ioprojecton/800W-load_bank/images/ac-dc.jpeg

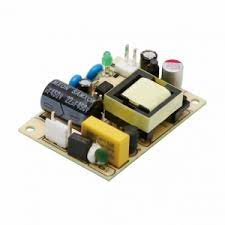
images/ac-dc.jpeg
