ioprojecton/800W-load_bank/images/fuse.jpeg

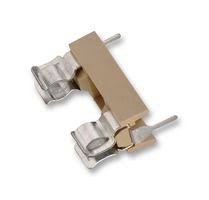
images/fuse.jpeg
