ioprojecton/800W-load_bank/images/LHD-03-TS.jpg

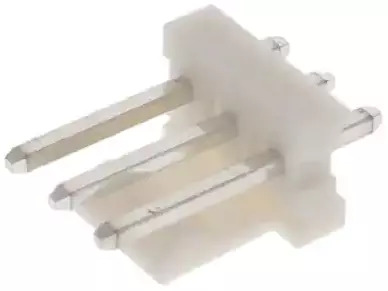
images/LHD-03-TS.jpg
