ioprojecton/800W-load_bank/images/npn.jpg

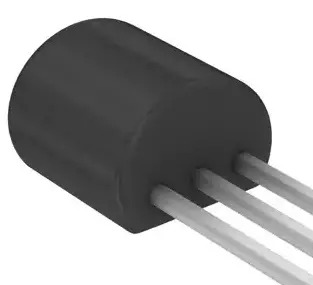
images/npn.jpg
