ioprojecton/800W-load_bank/images/resistor.jpg

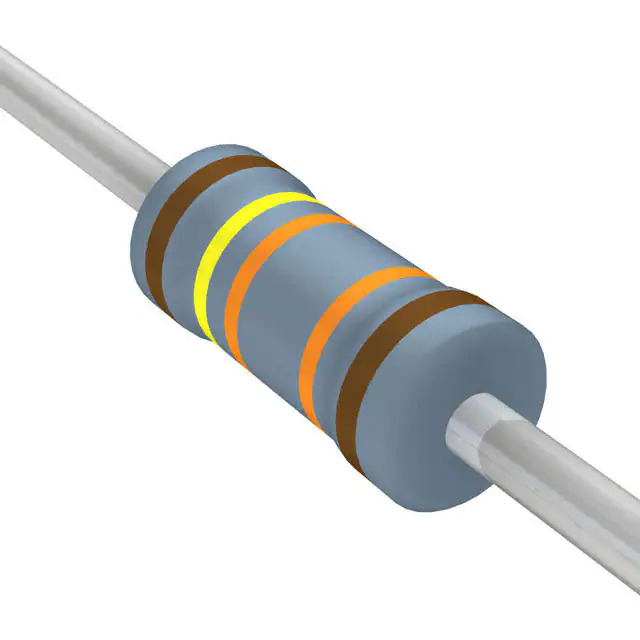
images/resistor.jpg
