ioprojecton/800W-load_bank/images/TC622-C4X-Regular.jpg

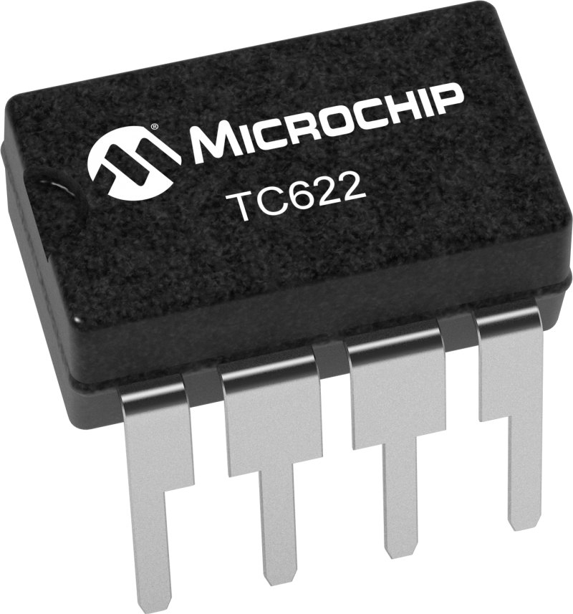
images/TC622-C4X-Regular.jpg
